reprappro/Huxley/images/coupling.jpg

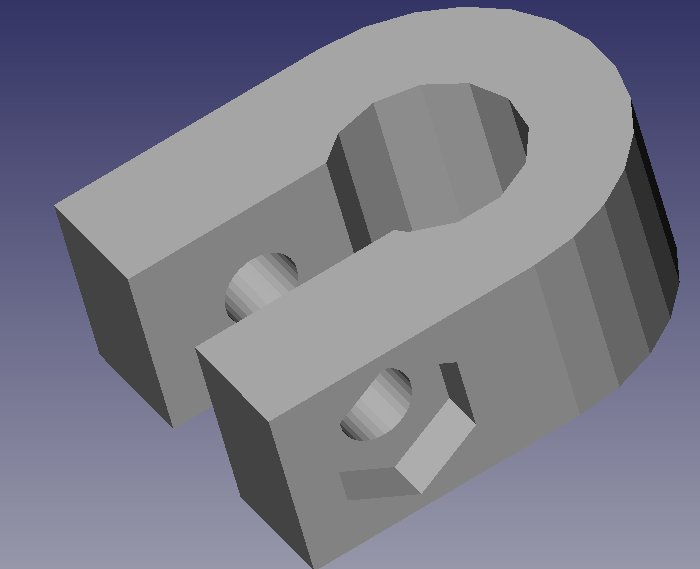
images/coupling.jpg
