reprappro/Huxley/SW/extruder/heatsink-block.SLDPRT

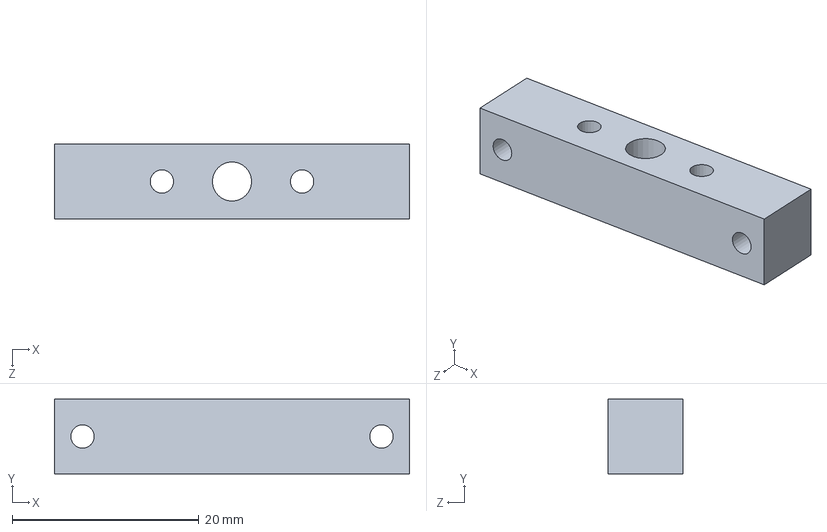
[picture p161: CAD file, 2013-06-18]
SW/extruder/heatsink-block.SLDPRT
38.0 x 8.00 x 8.00 mm
