reprappro/Huxley/dxf/frog.DXF

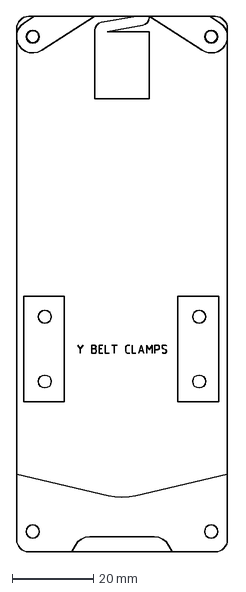
[picture p162: CAD file, 2012-03-14]
dxf/frog.DXF
52.6 x 132.1 mm
