reprappro/Huxley/Freecad/pulleys.fcstd

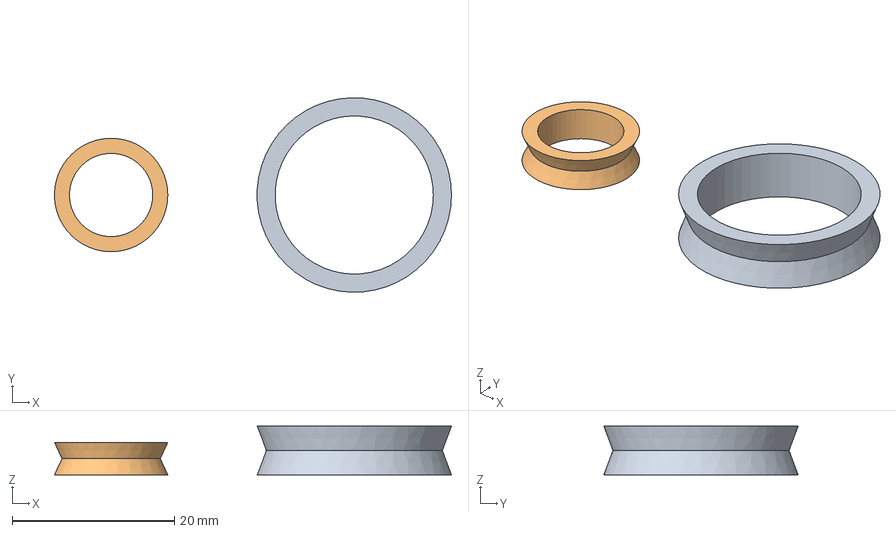
[picture p163: CAD file, 2014-09-25]
Freecad/pulleys.fcstd
49.0 x 24.0 x 6.00 mm
626-pulley
623-pulley
