reprappro/Huxley/Print-Huxley/Individual-STLs/pulley-2off.stl

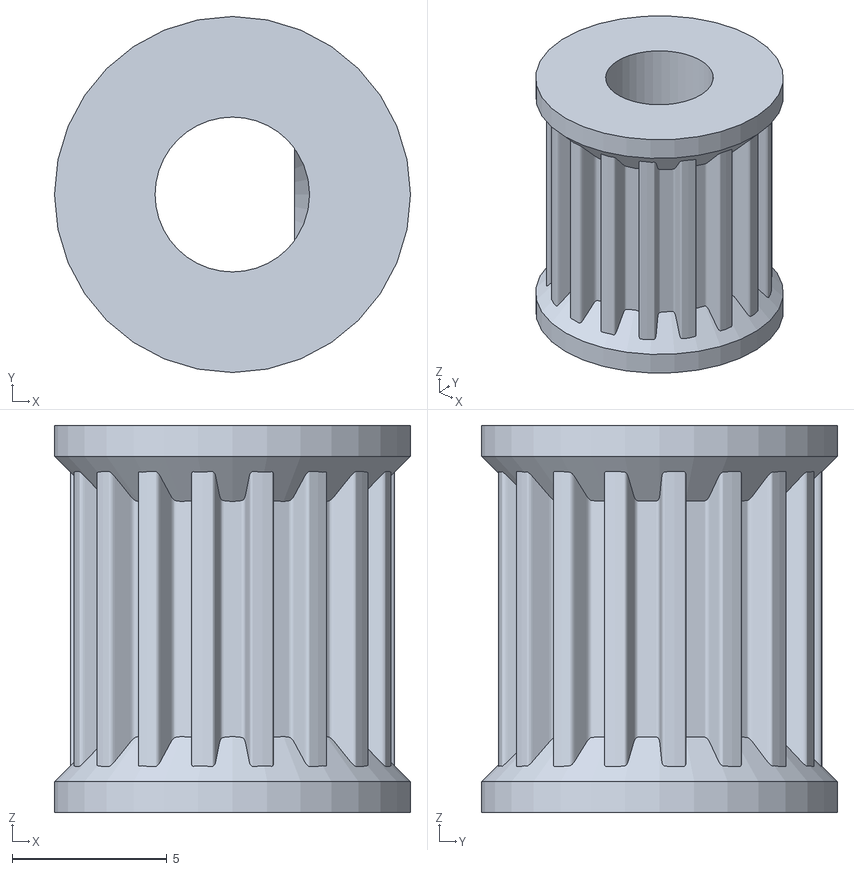
[picture p164: CAD file, 2013-08-01]
Print-Huxley/Individual-STLs/pulley-2off.stl
11.5 x 11.5 x 12.5
