reprappro/Huxley/step/bar-clamp.STEP

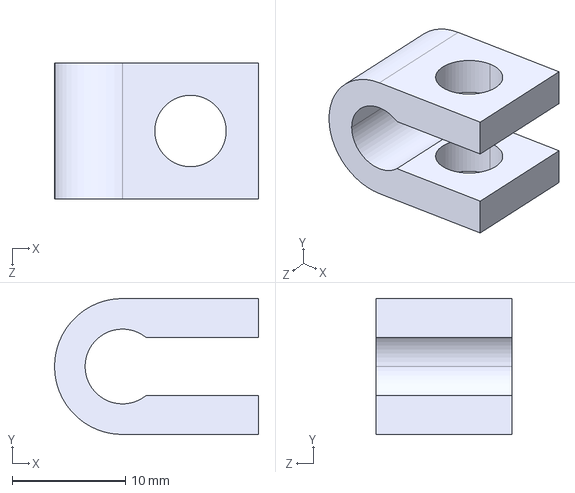
[picture p165: CAD file, 2012-05-29]
step/bar-clamp.STEP
18.0 x 12.0 x 12.0 mm
