reprappro/Huxley/SW/extruder/M6-Block.SLDPRT

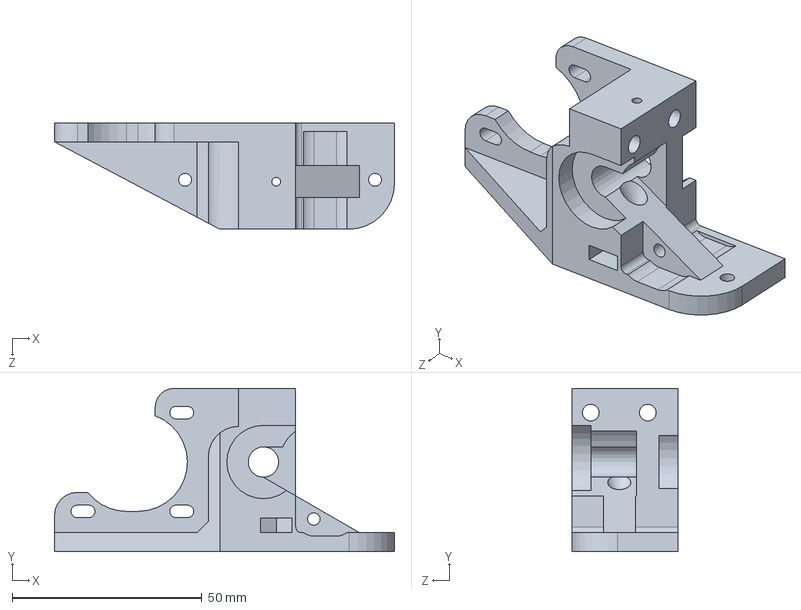
[picture p166: CAD file, 2013-04-22]
SW/extruder/M6-Block.SLDPRT
89.5 x 43.0 x 28.0 mm
