reprappro/Huxley/SW/fan-mount.SLDPRT

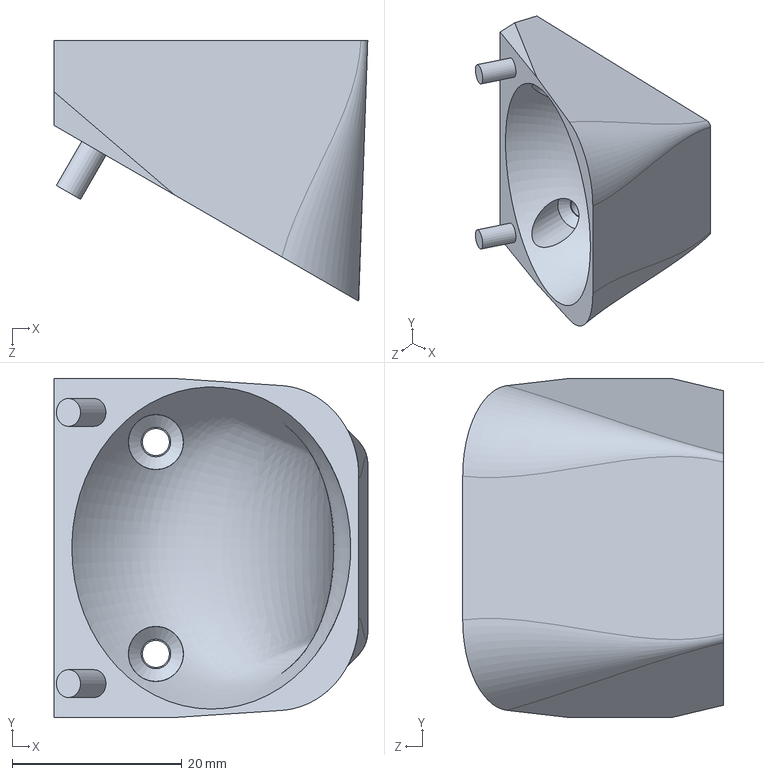
[picture p167: CAD file, 2013-06-18]
SW/fan-mount.SLDPRT
37.0 x 40.0 x 30.7 mm
