reprappro/Huxley/Freecad/bearing-runners.fcstd

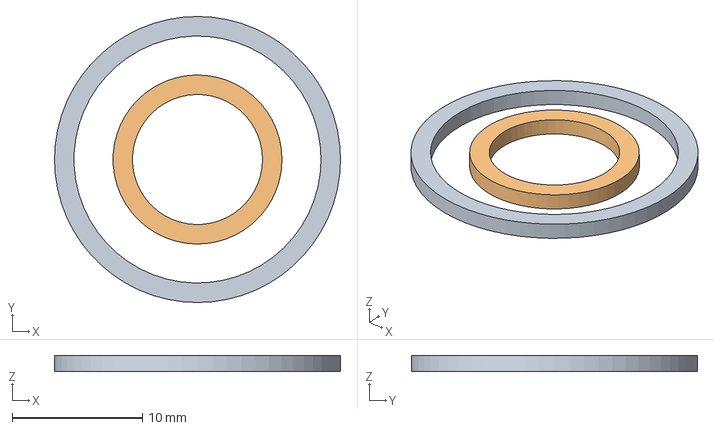
[picture p168: CAD file, 2014-09-25]
Freecad/bearing-runners.fcstd
22.0 x 22.0 x 1.25 mm
626-ridge
623-ridge
