reprappro/Huxley/step/bearing-holder-float.STEP

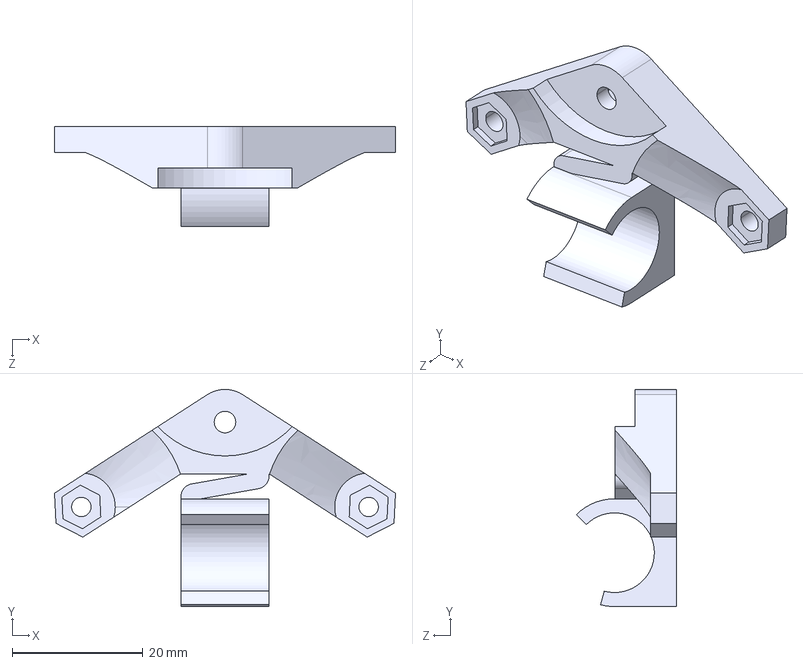
[picture p169: CAD file, 2012-05-29]
step/bearing-holder-float.STEP
52.2 x 33.2 x 15.3 mm
