reprappro/Huxley/SW/extruder-drive-holder.SLDPRT

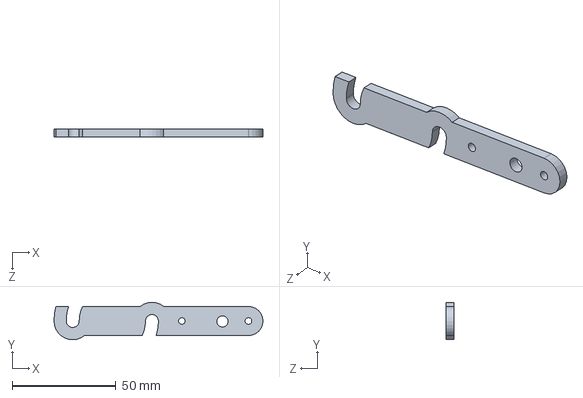
[picture p170: CAD file, 2013-05-24]
SW/extruder-drive-holder.SLDPRT
100.5 x 18.0 x 4.00 mm
