reprappro/Huxley/SW/extruder/nozzle-mounting.SLDPRT

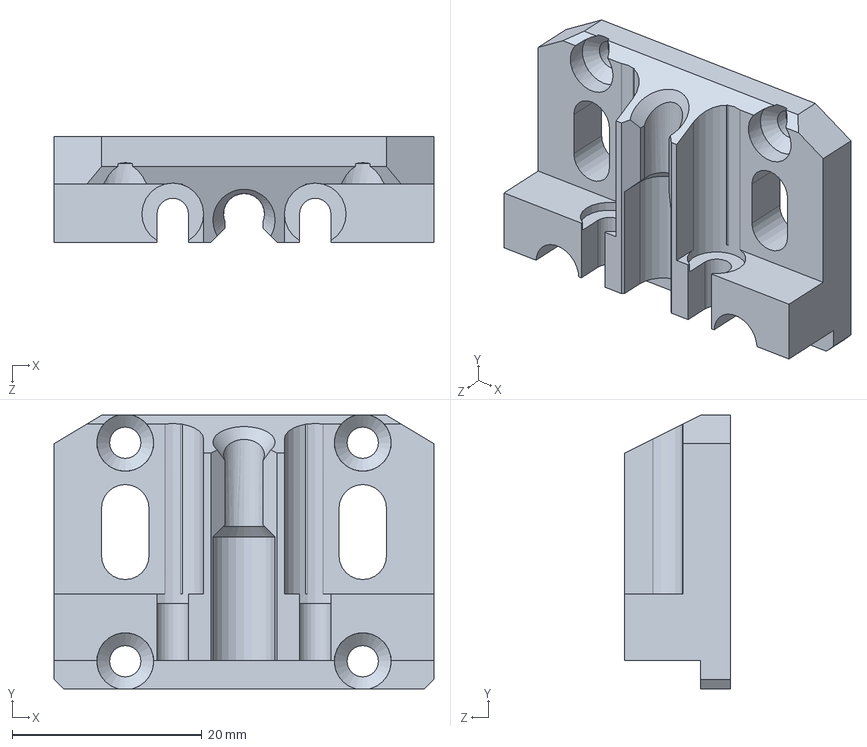
[picture p171: CAD file, 2013-04-22]
SW/extruder/nozzle-mounting.SLDPRT
40.0 x 28.8 x 11.1 mm
