reprappro/Huxley/Freecad/623.stl

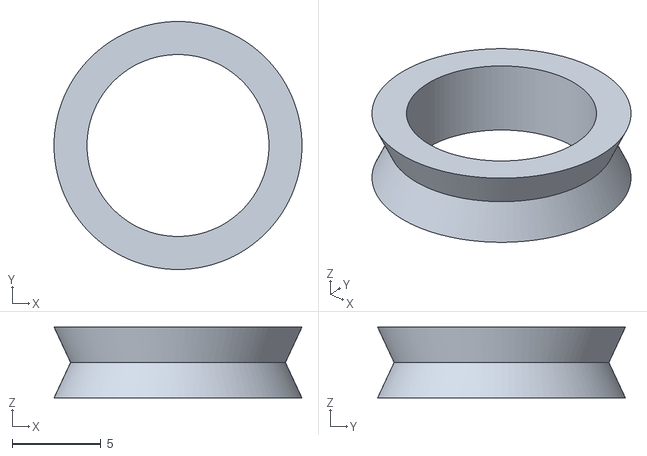
[picture p172: CAD file, 2014-09-25]
Freecad/623.stl
14.0 x 14.0 x 4.00
