reprappro/Huxley/step/x-idler-bracket.STEP

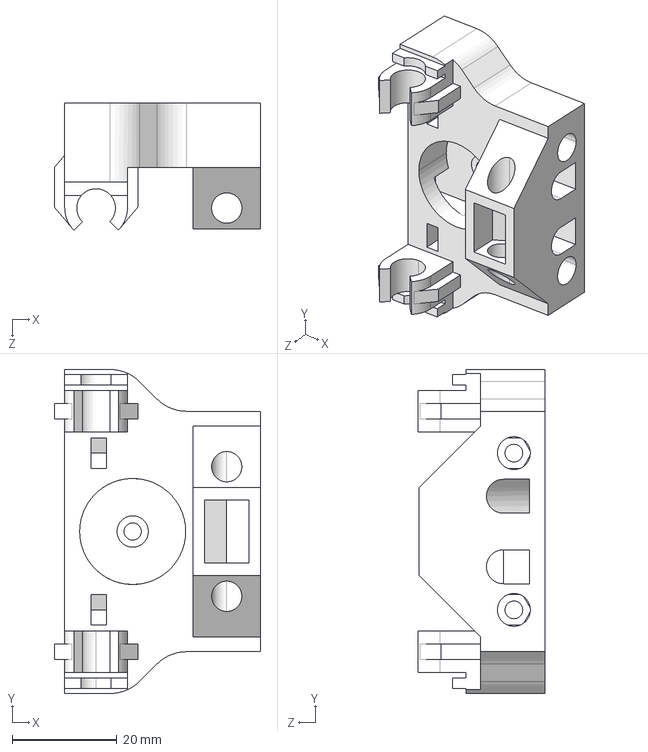
[picture p173: CAD file, 2012-05-29]
step/x-idler-bracket.STEP
39.5 x 62.0 x 24.4 mm
