reprappro/Huxley/SW/x-smooth-rod.SLDPRT

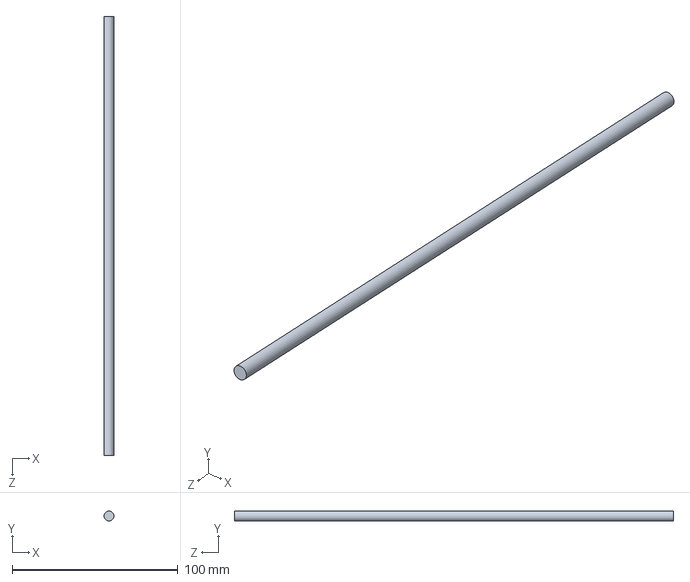
[picture p174: CAD file, 2013-04-22]
SW/x-smooth-rod.SLDPRT
6.00 x 6.00 x 265.0 mm
