reprappro/Huxley/Print-Huxley/Individual-STLs/y-idler-split1-1off.stl

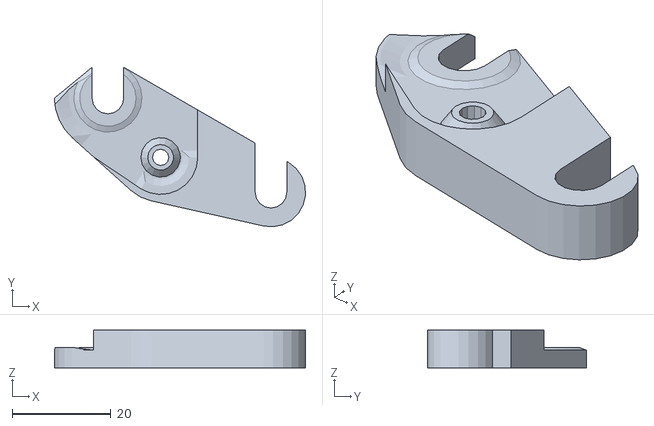
[picture p175: CAD file, 2013-04-22]
Print-Huxley/Individual-STLs/y-idler-split1-1off.stl
50.8 x 32.3 x 7.60
