reprappro/Huxley/SW/extruder/idler-bracket.SLDPRT

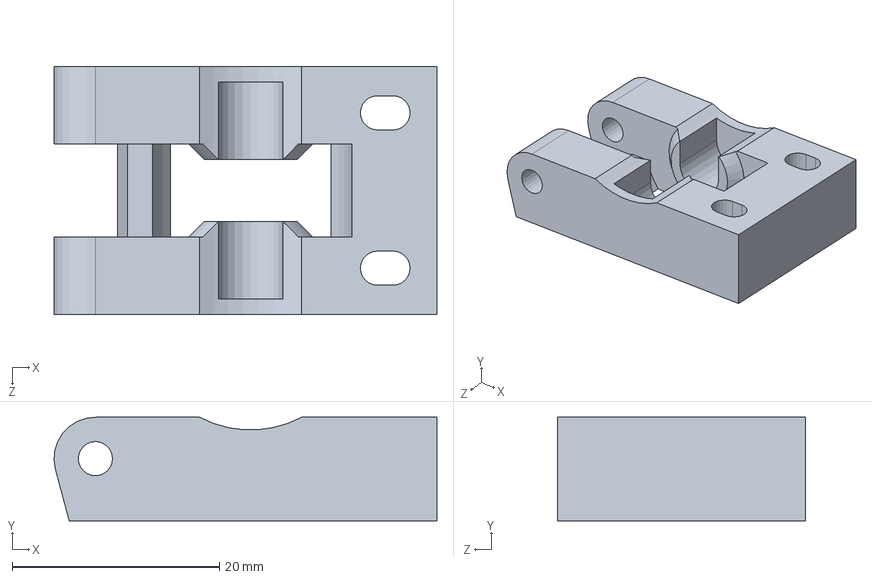
[picture p176: CAD file, 2013-04-22]
SW/extruder/idler-bracket.SLDPRT
37.0 x 10.0 x 24.0 mm
