reprappro/Huxley/SW/frog.SLDPRT

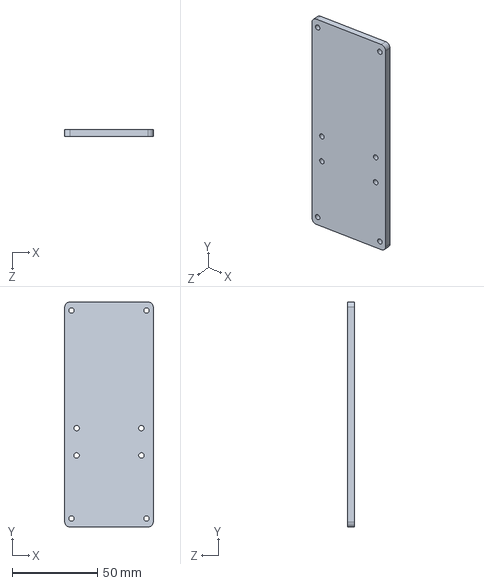
[picture p177: CAD file, 2013-04-22]
SW/frog.SLDPRT
52.0 x 132.0 x 4.00 mm
