reprappro/Huxley/Print-Huxley/Individual-STLs/y-motor-bracket.stl

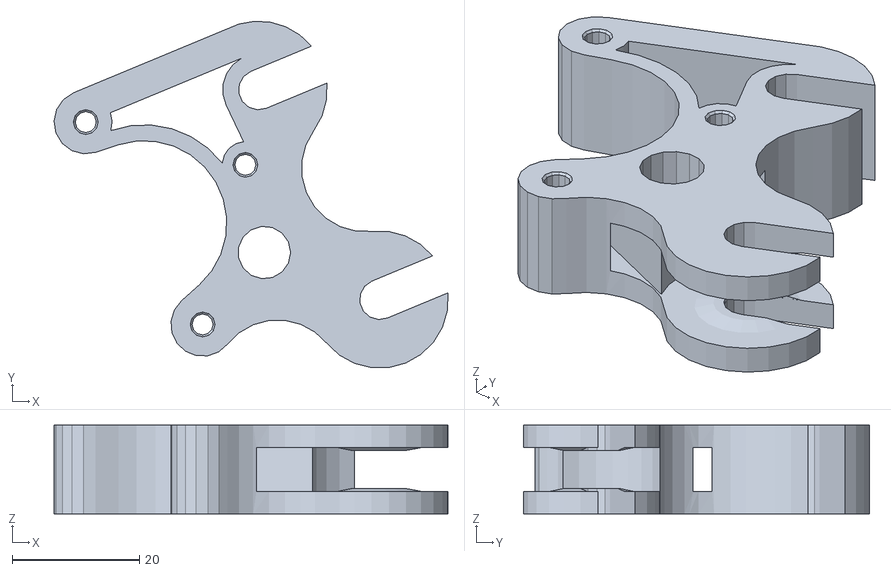
[picture p178: CAD file, 2013-04-22]
Print-Huxley/Individual-STLs/y-motor-bracket.stl
62.0 x 54.5 x 14.0
