reprappro/Huxley/step/y-belt-clamp.STEP

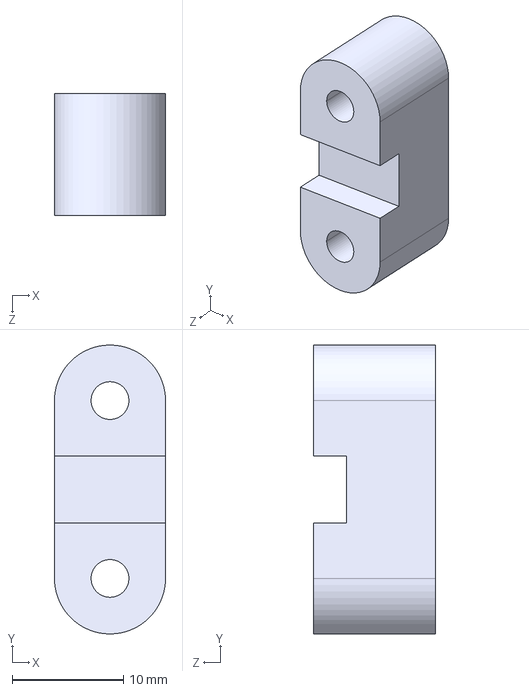
[picture p179: CAD file, 2012-05-29]
step/y-belt-clamp.STEP
10.0 x 26.0 x 11.0 mm
