reprappro/Huxley/SW/extruder/nozzle.SLDPRT

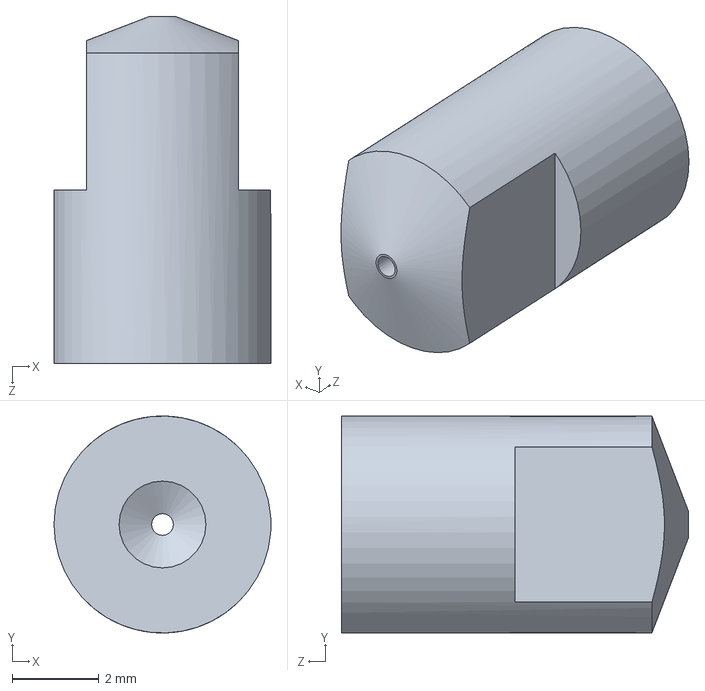
[picture p180: CAD file, 2012-05-29]
SW/extruder/nozzle.SLDPRT
5.00 x 5.00 x 8.00 mm
