reprappro/Huxley/SW/PCB.SLDPRT

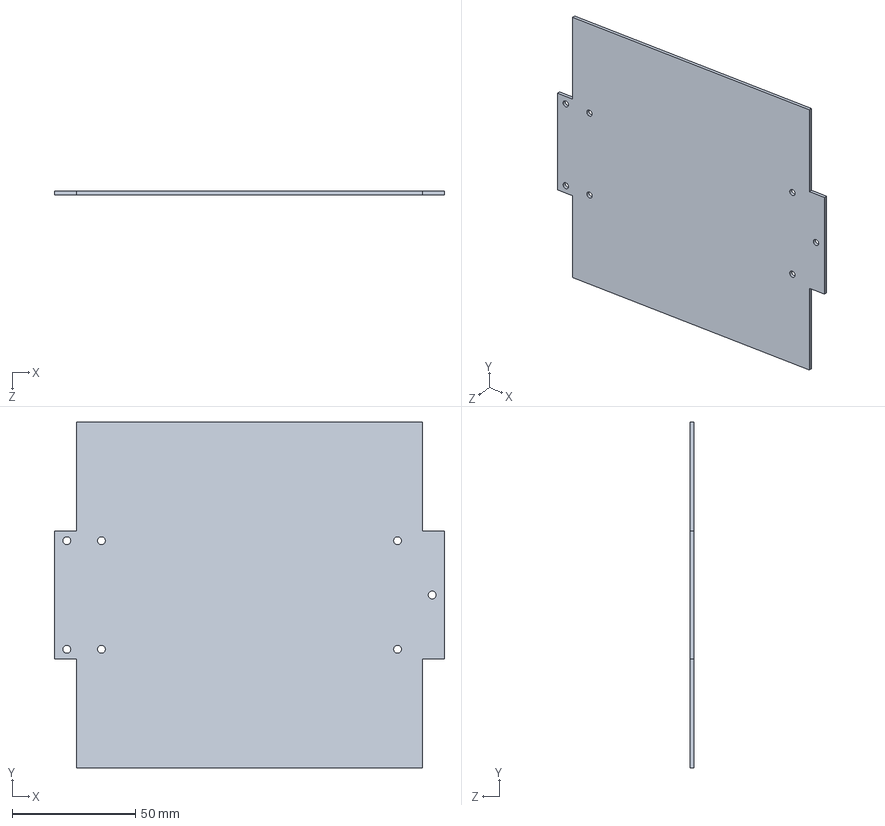
[picture p181: CAD file, 2013-04-22]
SW/PCB.SLDPRT
158.0 x 140.0 x 1.60 mm
