reprappro/Huxley/step/y-bar-clamp.STEP

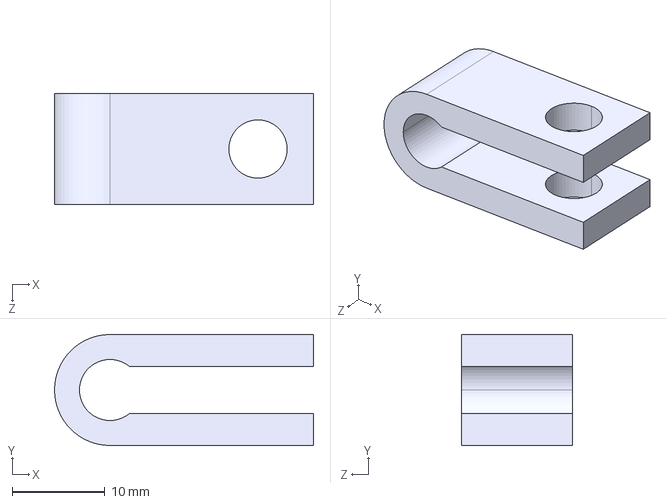
[picture p182: CAD file, 2012-05-29]
step/y-bar-clamp.STEP
28.0 x 12.0 x 12.0 mm
