reprappro/Huxley/SW/extruder/bowden-end.SLDPRT

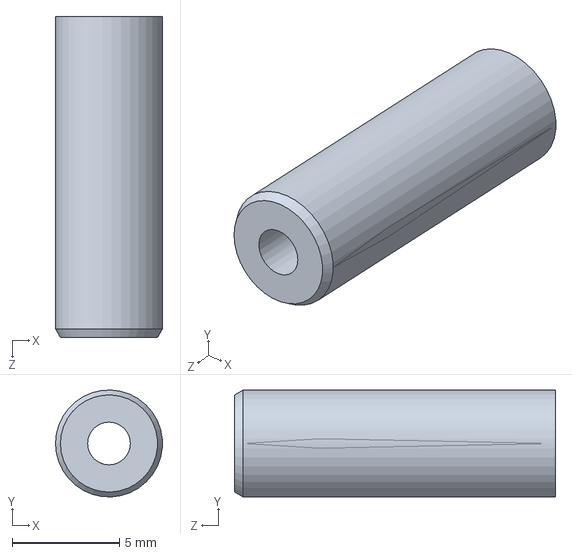
[picture p183: CAD file, 2012-05-29]
SW/extruder/bowden-end.SLDPRT
5.00 x 4.99 x 15.0 mm
