reprappro/Huxley/step/bearing-holder-fixed.STEP

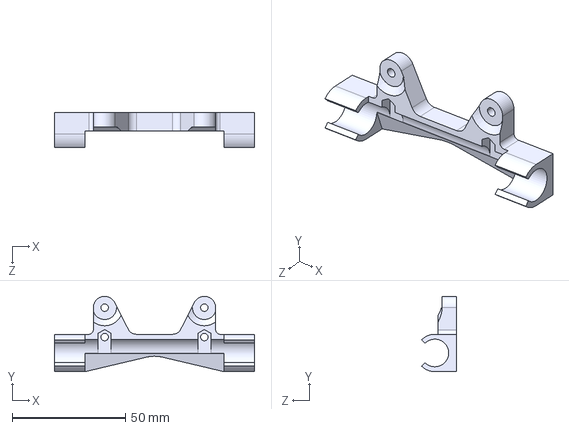
[picture p184: CAD file, 2012-05-29]
step/bearing-holder-fixed.STEP
88.3 x 33.2 x 15.3 mm
