reprappro/Huxley/SW/extruder/bowden-start.SLDPRT

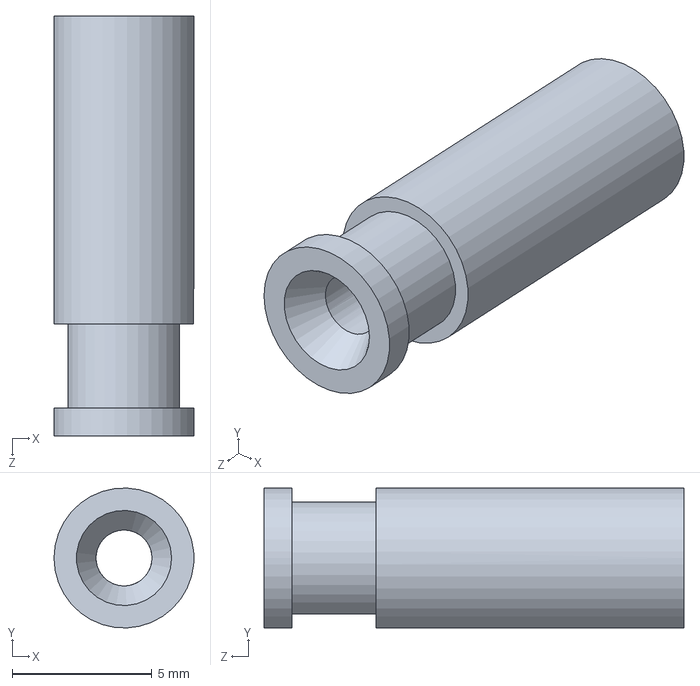
[picture p185: CAD file, 2012-05-29]
SW/extruder/bowden-start.SLDPRT
5.00 x 4.99 x 15.0 mm
