reprappro/Huxley/SW/frame-vertex-foot.SLDPRT

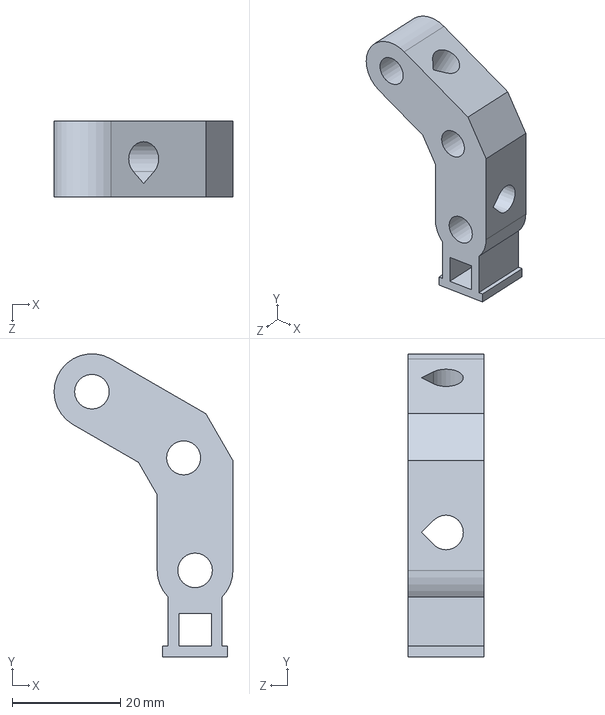
[picture p186: CAD file, 2013-04-22]
SW/frame-vertex-foot.SLDPRT
33.1 x 56.0 x 14.0 mm
