reprappro/Huxley/Print-Huxley/Individual-STLs/y-belt-tensioner-1off.stl

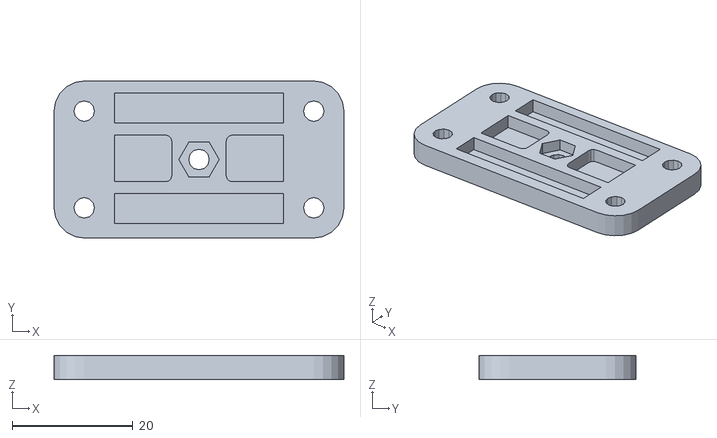
[picture p187: CAD file, 2013-04-22]
Print-Huxley/Individual-STLs/y-belt-tensioner-1off.stl
48.0 x 26.0 x 4.00
