reprappro/Huxley/step/y-endstop-holder.STEP

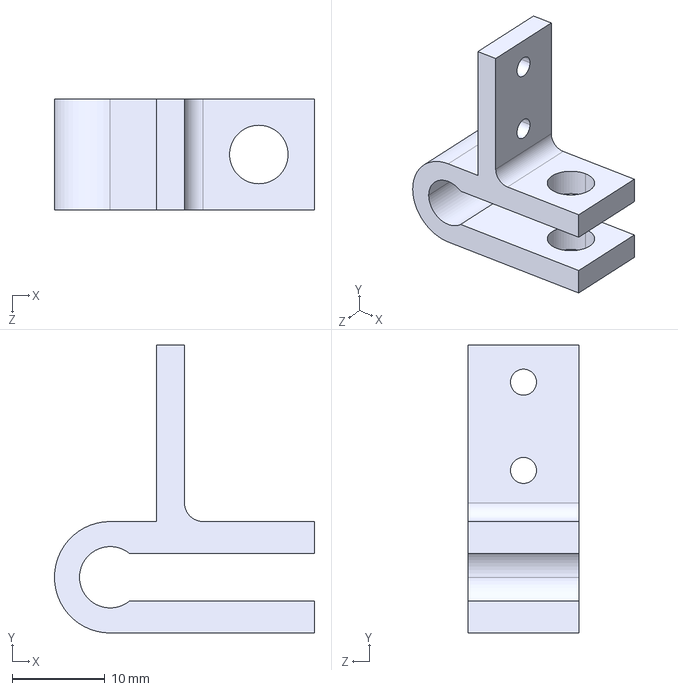
[picture p188: CAD file, 2012-05-29]
step/y-endstop-holder.STEP
28.0 x 31.0 x 12.0 mm
