reprappro/Huxley/SW/extruder/barrel.SLDPRT

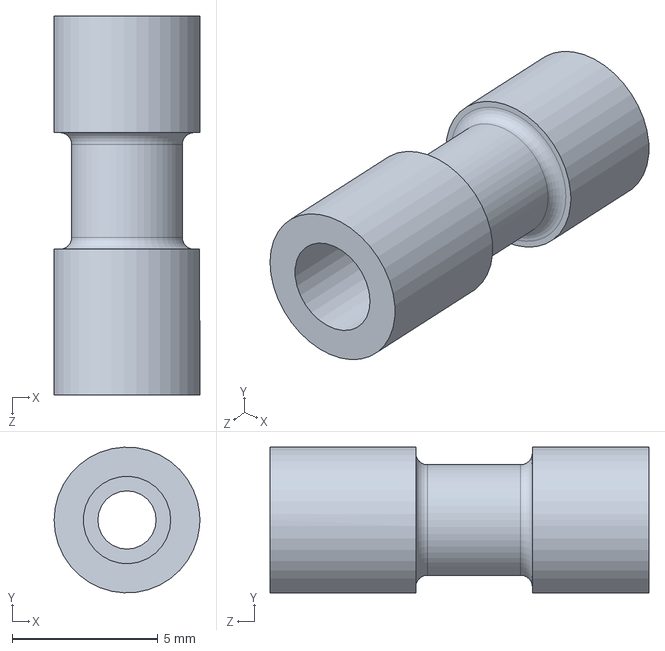
[picture p189: CAD file, 2012-05-29]
SW/extruder/barrel.SLDPRT
5.00 x 5.00 x 13.0 mm
