reprappro/Huxley/SW/v4-microswitch.SLDPRT

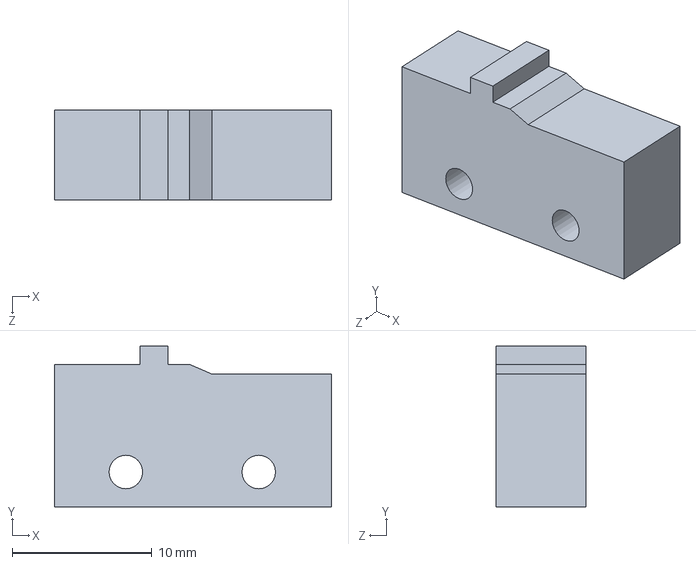
[picture p190: CAD file, 2013-04-22]
SW/v4-microswitch.SLDPRT
19.8 x 11.5 x 6.40 mm
