reprappro/Huxley/Print-Huxley/Individual-STLs/y-motor-split2-1off.stl

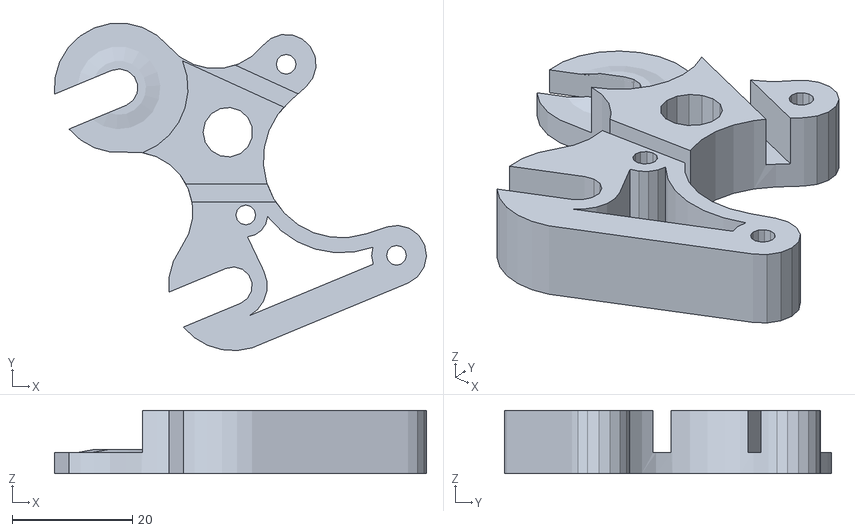
[picture p191: CAD file, 2013-04-22]
Print-Huxley/Individual-STLs/y-motor-split2-1off.stl
62.0 x 54.5 x 10.5
