reprappro/Huxley/Print-Huxley/Individual-STLs/pcb-clip-set.stl

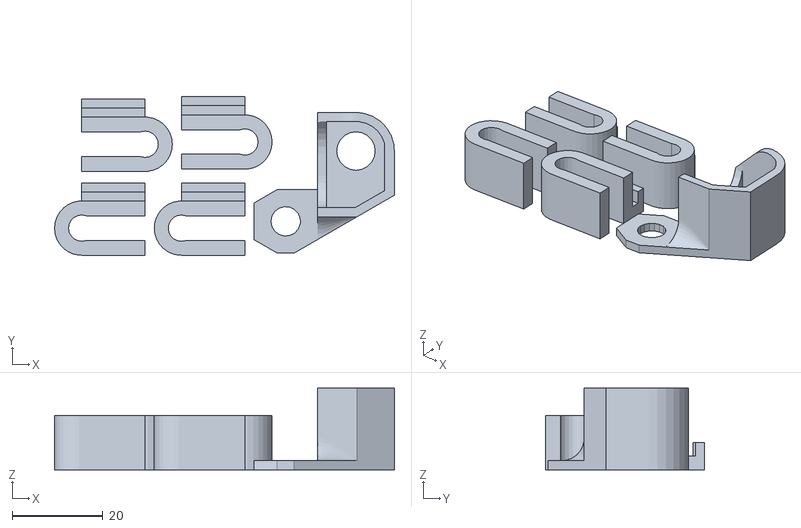
[picture p192: CAD file, 2013-04-22]
Print-Huxley/Individual-STLs/pcb-clip-set.stl
75.0 x 35.0 x 18.0
