reprappro/Huxley/SW/y-motor-bracket.SLDPRT

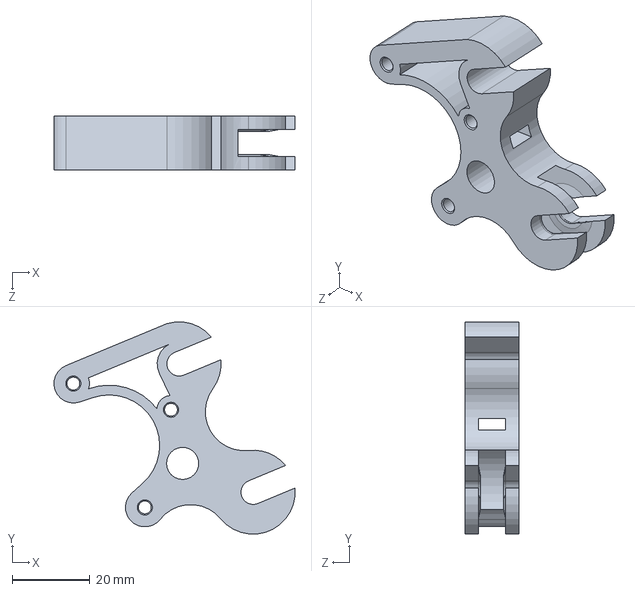
[picture p193: CAD file, 2013-04-22]
SW/y-motor-bracket.SLDPRT
62.0 x 54.5 x 14.0 mm
