reprappro/Huxley/Print-Huxley/Individual-STLs/power-bracket-1off.stl

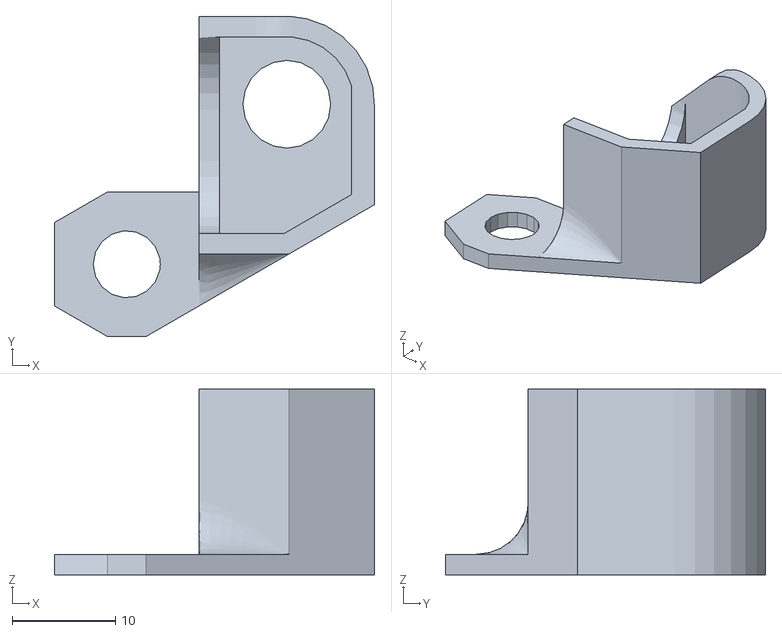
[picture p194: CAD file, 2013-04-22]
Print-Huxley/Individual-STLs/power-bracket-1off.stl
31.0 x 31.0 x 18.0
