reprappro/Huxley/SW/z-smooth-rod.SLDPRT

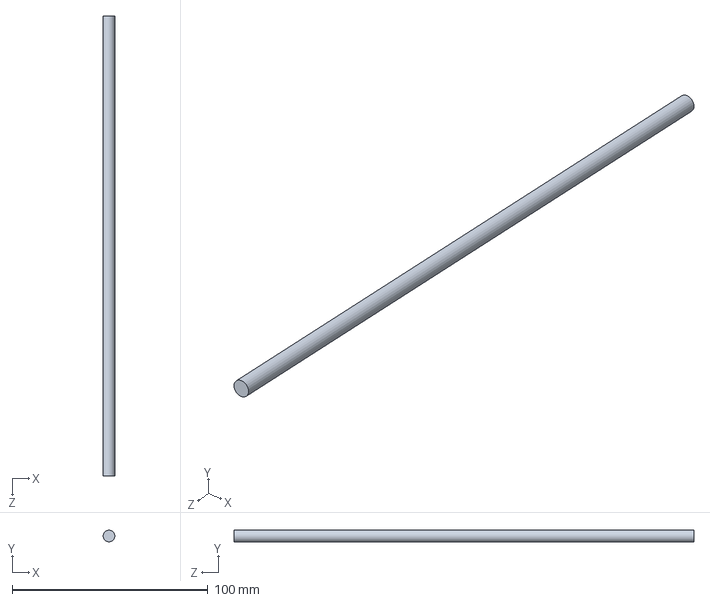
[picture p196: CAD file, 2013-04-22]
SW/z-smooth-rod.SLDPRT
6.00 x 6.00 x 235.0 mm
