reprappro/Huxley/Print-Huxley/Individual-STLs/y-idler-bracket.stl

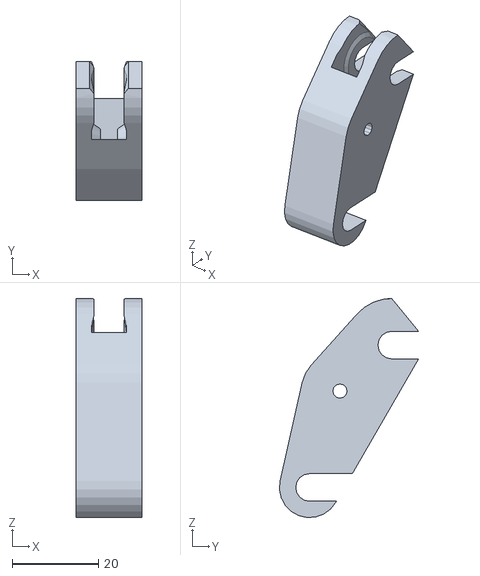
[picture p197: CAD file, 2013-04-22]
Print-Huxley/Individual-STLs/y-idler-bracket.stl
15.2 x 32.3 x 50.8
