reprappro/Huxley/SW/heat-spreader.SLDPRT

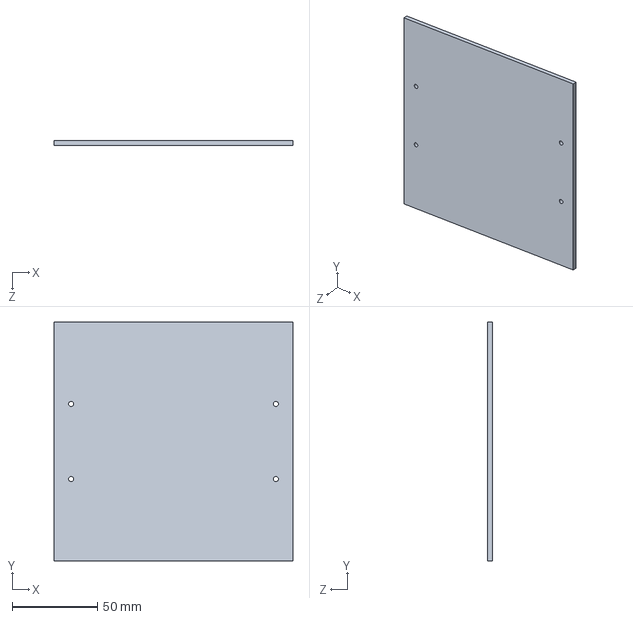
[picture p198: CAD file, 2013-04-22]
SW/heat-spreader.SLDPRT
140.0 x 140.0 x 3.00 mm
