reprappro/Huxley/Print-Huxley/Individual-STLs/x-carriage-1off.stl

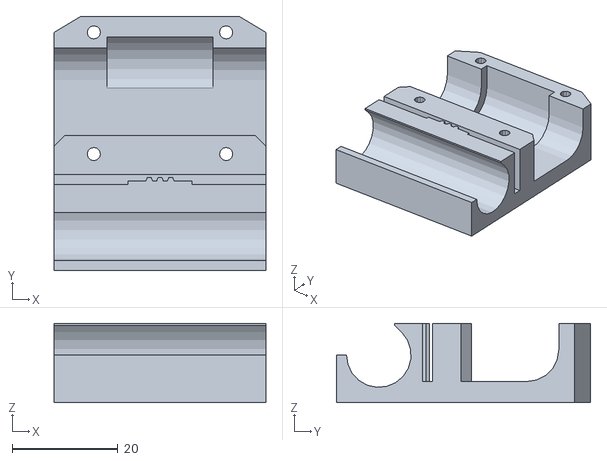
[picture p199: CAD file, 2013-04-22]
Print-Huxley/Individual-STLs/x-carriage-1off.stl
40.0 x 48.0 x 15.0
