reprappro/Huxley/SW/idler-cover.SLDPRT

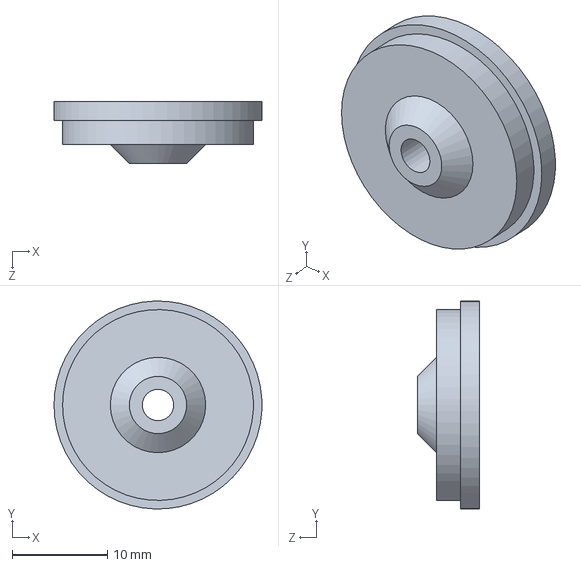
[picture p200: CAD file, 2013-04-22]
SW/idler-cover.SLDPRT
21.8 x 21.8 x 6.50 mm
