reprappro/Huxley/SW/LM6UU.SLDPRT

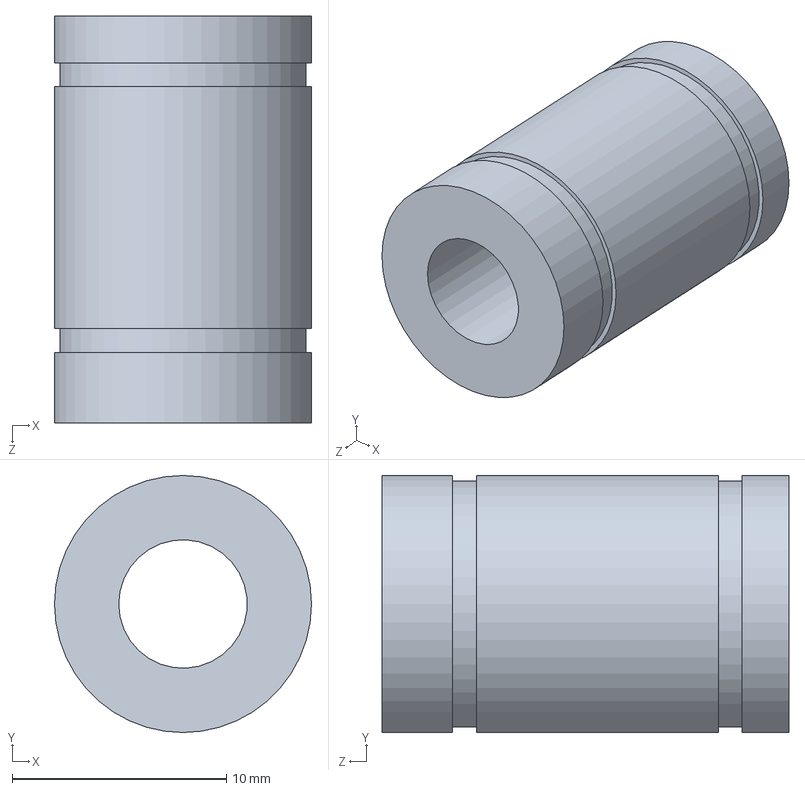
[picture p201: CAD file, 2013-04-22]
SW/LM6UU.SLDPRT
12.0 x 12.0 x 19.0 mm
