reprappro/Huxley/SW/frame-vertex.SLDPRT

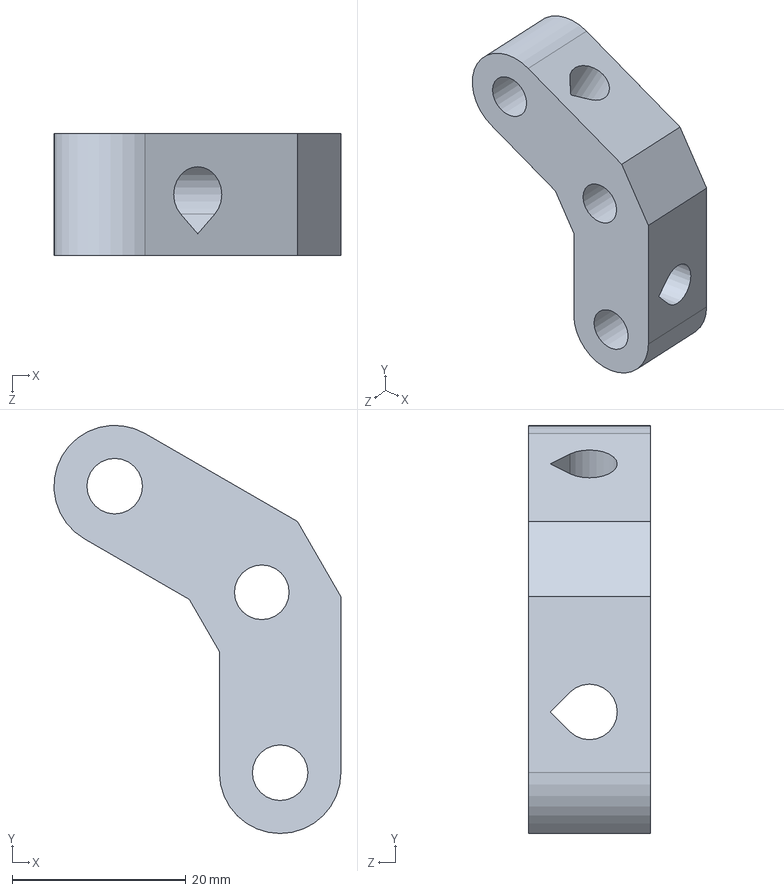
[picture p202: CAD file, 2013-04-22]
SW/frame-vertex.SLDPRT
33.0 x 47.0 x 14.0 mm
