reprappro/Huxley/Print-Huxley/Individual-STLs/coupling-4off.stl

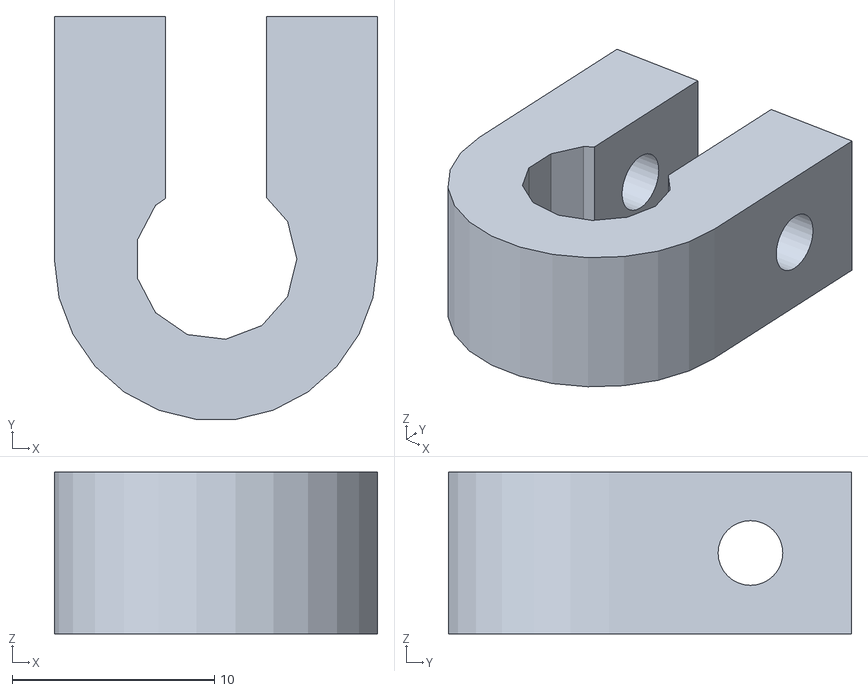
[picture p203: CAD file, 2012-05-29]
Print-Huxley/Individual-STLs/coupling-4off.stl
16.0 x 19.9 x 8.00
