reprappro/Huxley/SW/y-smooth-rod.SLDPRT

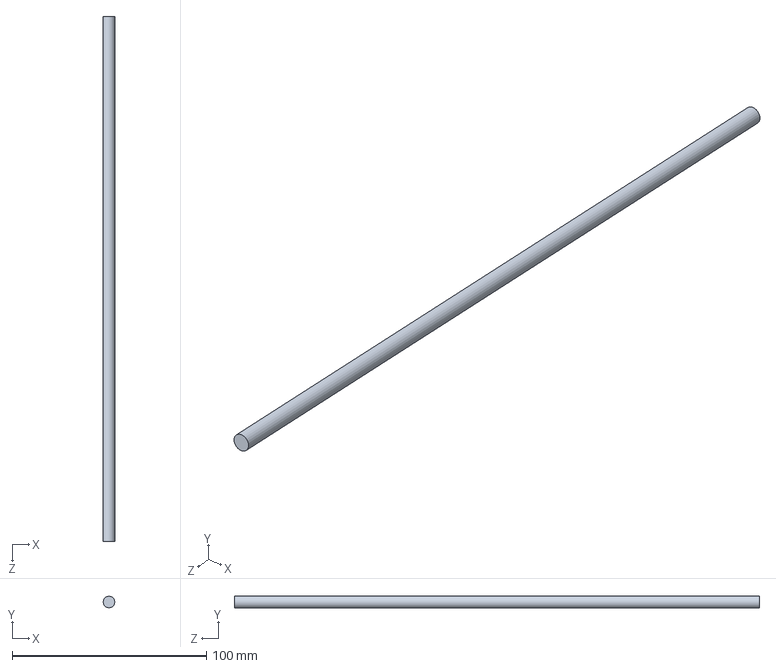
[picture p204: CAD file, 2013-04-22]
SW/y-smooth-rod.SLDPRT
6.00 x 6.00 x 270.0 mm
