reprappro/Huxley/Print-Huxley/Individual-STLs/z-motor-bracket-2off.stl

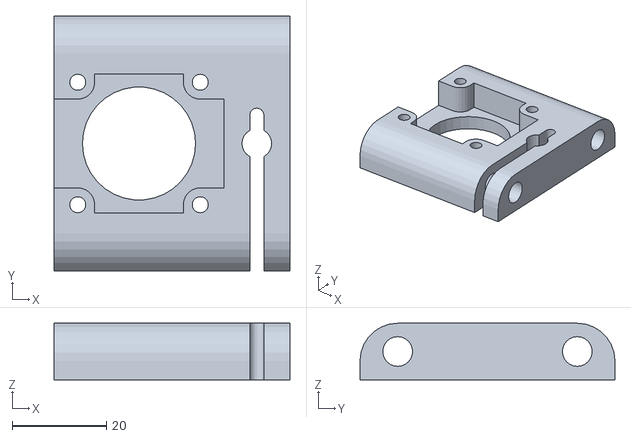
[picture p205: CAD file, 2012-01-18]
Print-Huxley/Individual-STLs/z-motor-bracket-2off.stl
50.0 x 54.1 x 12.0
