reprappro/Huxley/Print-Huxley/Individual-STLs/pcb-clip-left-2off.stl

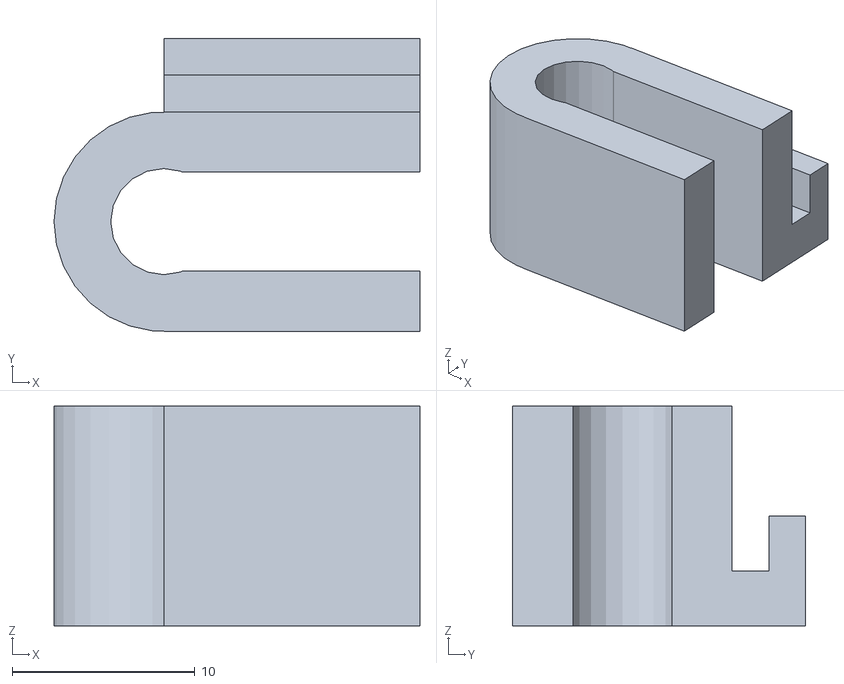
[picture p206: CAD file, 2012-01-18]
Print-Huxley/Individual-STLs/pcb-clip-left-2off.stl
20.0 x 16.0 x 12.0
