reprappro/Huxley/SW/bed-heat-shield.SLDPRT

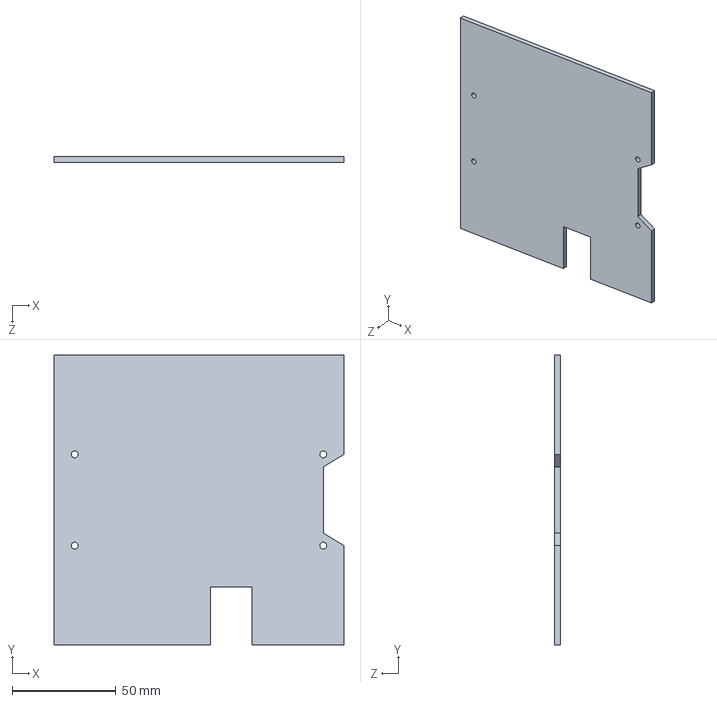
[picture p207: CAD file, 2013-04-22]
SW/bed-heat-shield.SLDPRT
140.0 x 140.0 x 3.00 mm
