reprappro/Huxley/SW/624-bearing.sldprt

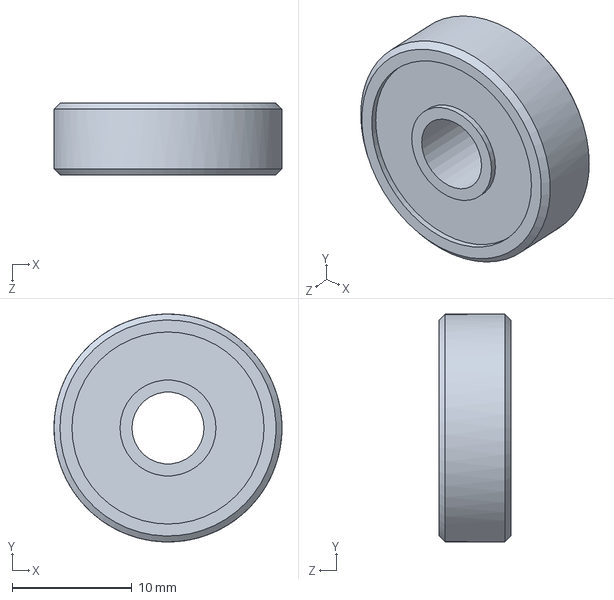
[picture p208: CAD file, 2013-04-22]
SW/624-bearing.sldprt
19.0 x 19.0 x 6.00 mm
