reprappro/Huxley/Print-Huxley/Individual-STLs/z-endstop-holder-1off.stl

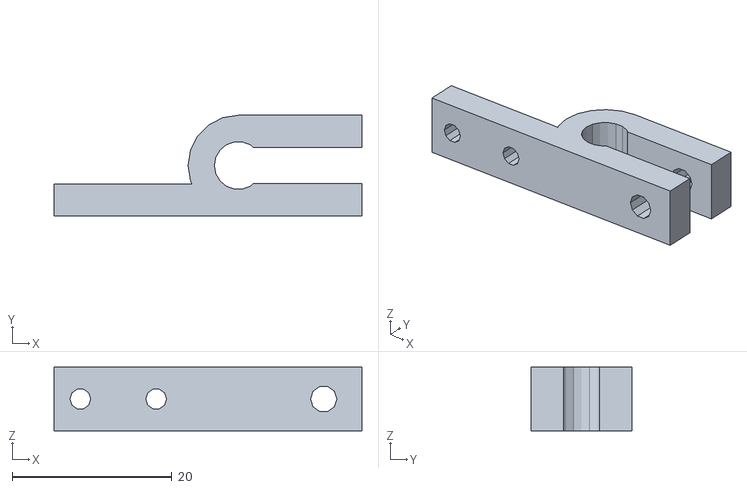
[picture p209: CAD file, 2012-01-18]
Print-Huxley/Individual-STLs/z-endstop-holder-1off.stl
38.6 x 12.6 x 8.00
