reprappro/Huxley/SW/T2_5x16-drive-pulley 00.sldprt

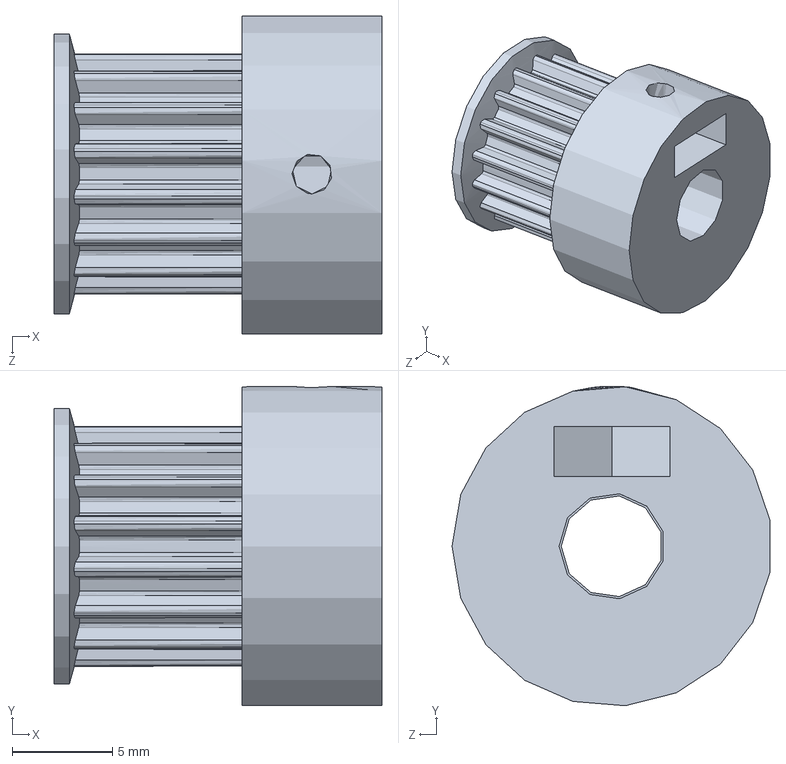
[picture p210: CAD file, 2013-04-22]
SW/T2_5x16-drive-pulley 00.sldprt
16.4 x 16.0 x 15.9 mm
