reprappro/Huxley/Print-Huxley/Mendel-trays-STLs/Mendel-Tray-2_stl.scad

translate([26,124,-0.0]) rotate([0,0,-90]) import_stl("/home/jeanmarc/Documents/Models/RepRapPro/Huxley/Print-Huxley/Individual-STLs/extruder-drive-holder.stl");
translate([49,65,5.0]) rotate([0,0,-90]) import_stl("/home/jeanmarc/Documents/Models/RepRapPro/Extruder-drive/Print-extruder-drive/Individual-STLs/frame-clip-2off.stl");
translate([146,30,-0.0]) rotate([0,0,0]) import_stl("/home/jeanmarc/Documents/Models/RepRapPro/Huxley/Print-Huxley/Individual-STLs/y-belt-clamp.stl");
translate([178,176,-9.1461e-18]) rotate([0,0,270]) import_stl("/home/jeanmarc/Documents/Models/RepRapPro/Huxley/Print-Huxley/Individual-STLs/y-motor-split1.stl");
translate([40,163,-0.0]) rotate([0,0,90]) import_stl("/home/jeanmarc/Documents/Models/RepRapPro/Huxley/Print-Huxley/Individual-STLs/pcb-clip-right.stl");
translate([138,94,-6.02984e-18]) rotate([0,0,30]) import_stl("/home/jeanmarc/Documents/Models/RepRapPro/Huxley/Print-Huxley/Individual-STLs/y-idler-split1.stl");
translate([135,101,-6.02984e-18]) rotate([0,0,150]) import_stl("/home/jeanmarc/Documents/Models/RepRapPro/Huxley/Print-Huxley/Individual-STLs/y-idler-split2.stl");
translate([131,66,0]) rotate([0,0,90]) import_stl("/home/jeanmarc/Documents/Models/RepRapPro/Huxley/Print-Huxley/Individual-STLs/coupling.stl");
translate([59,88,-0.0]) rotate([0,0,0]) import_stl("/home/jeanmarc/Documents/Models/RepRapPro/Huxley/Print-Huxley/Individual-STLs/y-bar-clamp.stl");
translate([49,139,-0.0]) rotate([0,0,-90]) import_stl("/home/jeanmarc/Documents/Models/RepRapPro/Huxley/Print-Huxley/Individual-STLs/pcb-clip-left.stl");
translate([165,39,5.0]) rotate([0,0,90]) import_stl("/home/jeanmarc/Documents/Models/RepRapPro/Extruder-drive/Print-extruder-drive/Individual-STLs/frame-clip-2off.stl");
translate([97,29,-0.0]) rotate([0,0,0]) import_stl("/home/jeanmarc/Documents/Models/RepRapPro/Huxley/Print-Huxley/Individual-STLs/y-belt-tensioner.stl");
translate([59,102,0]) rotate([0,0,0]) import_stl("/home/jeanmarc/Documents/Models/RepRapPro/Huxley/Print-Huxley/Individual-STLs/y-bar-clamp.stl");
translate([163,94,-0.0]) rotate([0,0,0]) import_stl("/home/jeanmarc/Documents/Models/RepRapPro/Extruder-drive/Print-extruder-drive/Individual-STLs/spacer-1off.stl");
translate([33,139,-0.0]) rotate([0,0,90]) import_stl("/home/jeanmarc/Documents/Models/RepRapPro/Huxley/Print-Huxley/Individual-STLs/pcb-clip-right.stl");
translate([84,159,5.0]) rotate([0,0,0]) import_stl("/home/jeanmarc/Documents/Models/RepRapPro/Extruder-drive/Print-extruder-drive/Individual-STLs/frame-clip-tab-1off.stl");
translate([129,157,-0.0]) rotate([0,0,90]) import_stl("/home/jeanmarc/Documents/Models/RepRapPro/Huxley/Print-Huxley/Individual-STLs/power-bracket.stl");
translate([70,173,-0.0]) rotate([0,0,80]) import_stl("/home/jeanmarc/Documents/Models/RepRapPro/Huxley/Print-Huxley/Individual-STLs/y-motor-split2.stl");
translate([176,66,0]) rotate([0,0,-270]) import_stl("/home/jeanmarc/Documents/Models/RepRapPro/Huxley/Print-Huxley/Individual-STLs/coupling.stl");
translate([105,66,-0.0]) rotate([0,0,-90]) import_stl("/home/jeanmarc/Documents/Models/RepRapPro/Huxley/Print-Huxley/Individual-STLs/coupling.stl");
translate([149,66,0]) rotate([0,0,-90]) import_stl("/home/jeanmarc/Documents/Models/RepRapPro/Huxley/Print-Huxley/Individual-STLs/coupling.stl");
translate([146,123,-0.0]) rotate([0,0,-180]) import_stl("/home/jeanmarc/Documents/Models/RepRapPro/Huxley/Print-Huxley/Individual-STLs/y-endstop-holder.stl");
translate([175,30,-0.0]) rotate([0,0,0]) import_stl("/home/jeanmarc/Documents/Models/RepRapPro/Huxley/Print-Huxley/Individual-STLs/y-belt-clamp.stl");
translate([55,162,-0.0]) rotate([0,0,-90]) import_stl("/home/jeanmarc/Documents/Models/RepRapPro/Huxley/Print-Huxley/Individual-STLs/pcb-clip-left.stl");
translate([46,116,0]) rotate([0,0,-90]) import_stl("/home/jeanmarc/Documents/Models/RepRapPro/Huxley/Print-Huxley/Individual-STLs/y-bar-clamp.stl");
